Maya-R14/Rubix-Cube-Solver-2022/3D Modeling/Technical Drawings/PNGs/Maya A. Rosales O._Solver_Technical Sheet-4.png

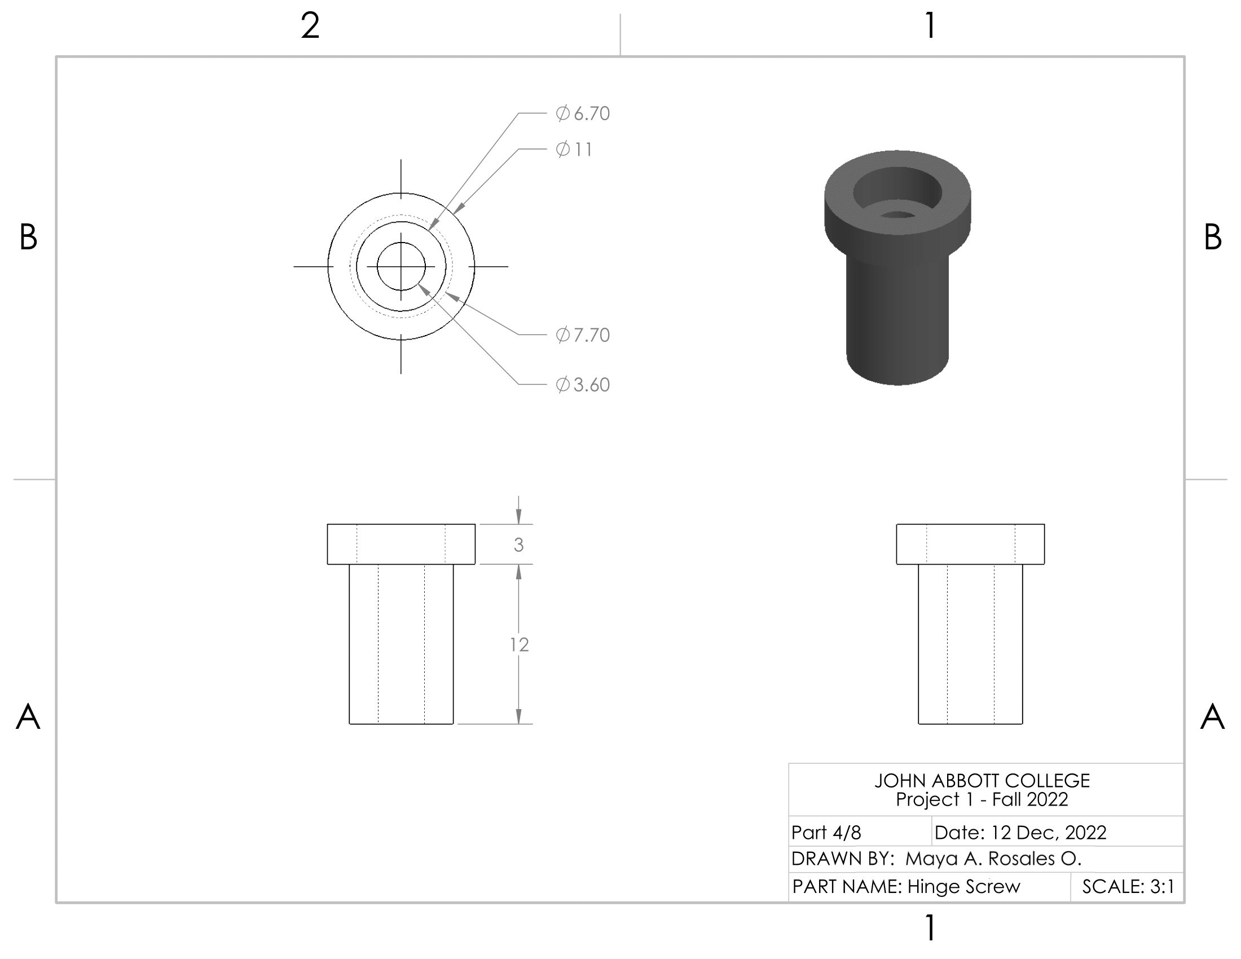
3D Modeling/Technical Drawings/PNGs/Maya A. Rosales O._Solver_Technical Sheet-4.png
