Maya-R14/Rubix-Cube-Solver-2022/3D Modeling/Parts/Part - Top Arm - Camera Housing.SLDPRT

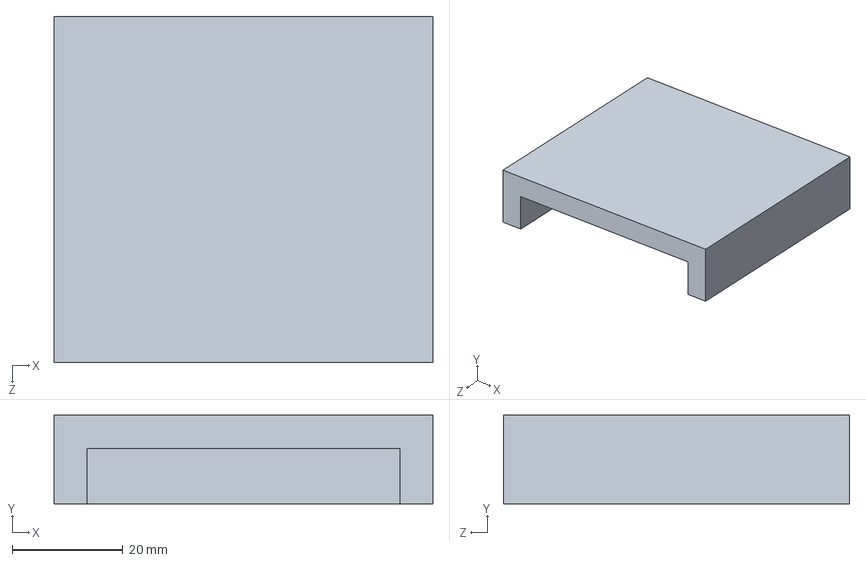
[picture p27: CAD file, 2025-12-05]
3D Modeling/Parts/Part - Top Arm - Camera Housing.SLDPRT
68.5 x 16.0 x 62.5 mm
