Maya-R14/Rubix-Cube-Solver-2022/3D Modeling/References/REFERENCE - PI.SLDPRT

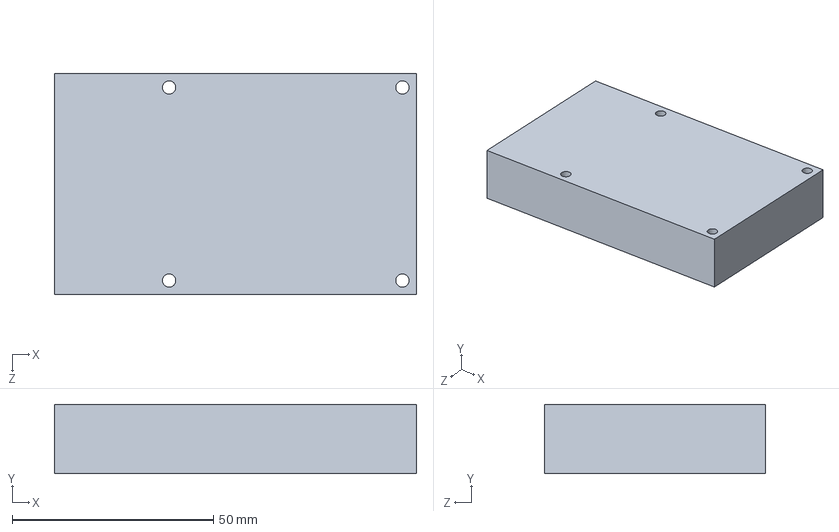
[picture p28: CAD file, 2025-12-05]
3D Modeling/References/REFERENCE - PI.SLDPRT
90.0 x 17.2 x 55.0 mm
