Maya-R14/Rubix-Cube-Solver-2022/3D Modeling/Parts/Part - Hinge - Screw.SLDPRT

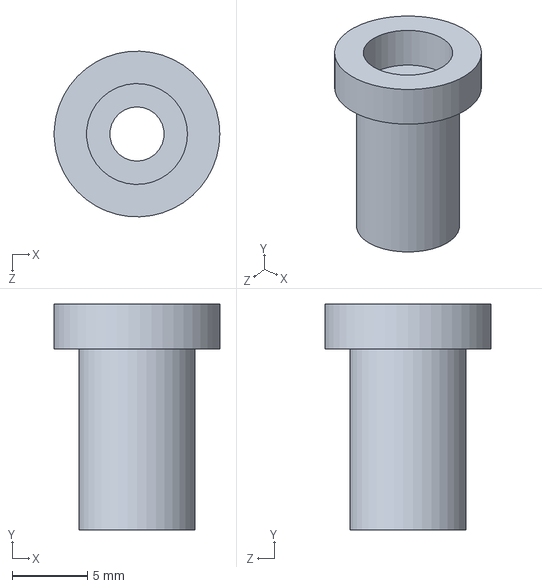
[picture p29: CAD file, 2025-12-05]
3D Modeling/Parts/Part - Hinge - Screw.SLDPRT
11.0 x 15.0 x 11.0 mm
